ioquatix/window-latch/photos/IMG_9571.jpg

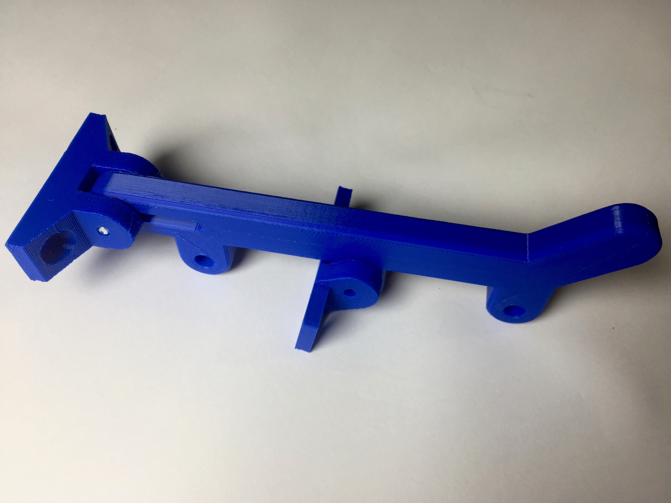
photos/IMG_9571.jpg
